GiacoBot/ESP32MP3/Software/src/AppState.h

#ifndef APP_STATE_H
#define APP_STATE_H

// Defines the current active screen or view of the application.
enum class AppScreen {
    SCREEN_BLUETOOTH_SELECTION,
    SCREEN_TRACK_SELECTION,
    SCREEN_NOW_PLAYING,
    SCREEN_VOLUME_CONTROL
};

#endif // APP_STATE_H
