GiacoBot/ESP32MP3/Software/src/DisplayManager.h

#ifndef DISPLAY_MANAGER_H
#define DISPLAY_MANAGER_H

#include <U8g2lib.h>
#include "settings.h"
#include "AppState.h"
#include "MusicPlayer.h"
#include "BluetoothManager.h"
#include "PlaylistManager.h"

class DisplayManager {
public:
    DisplayManager();
    bool initialize();

    // --- Core Update Method ---
    // This is now the main entry point for drawing, dispatched by the main loop.
    void update(AppScreen current_screen);

    // --- Setters for Managers ---
    void setMusicPlayer(MusicPlayer* player);
    void setBluetoothManager(BluetoothManager* btManager);
    void setPlaylistManager(PlaylistManager* playlistManager);

    // --- Setters for UI State ---
    // These will be called from the main loop to update the UI state
    void setBluetoothMenuState(int selected_index, int scroll_offset);
    void setPlaylistMenuState(int selected_index, int scroll_offset);

private:
    // --- Managers ---
    MusicPlayer* music_player;
    BluetoothManager* bluetooth_manager;
    PlaylistManager* playlist_manager;

    // --- Display & State ---
    U8G2_DISPLAY_TYPE u8g2;
    bool is_initialized;

    // --- UI State Variables ---
    int bt_menu_selected_index;
    int bt_menu_scroll_offset;
    int playlist_menu_selected_index;
    int playlist_menu_scroll_offset;

    // Internal state for tracking scroll direction
    int prev_bt_menu_selected_index;
    int prev_playlist_menu_selected_index;

    // Internal state for horizontal text scrolling
    unsigned long bt_last_selection_time;
    unsigned long bt_last_scroll_time;
    int bt_text_scroll_offset_pixels;
    unsigned long playlist_last_selection_time;
    unsigned long playlist_last_scroll_time;
    int playlist_text_scroll_offset_pixels;

    // Track name cache for playlist menu
    static const int PLAYLIST_VISIBLE_ITEMS = 4;
    String playlist_cached_names[PLAYLIST_VISIBLE_ITEMS];
    int playlist_cache_start_index;  // -1 = cache invalid

    // --- Drawing Methods ---
    void drawBluetoothMenu();
    void drawPlaylistMenu();
    void drawNowPlayingScreen();
    void drawVolumeScreen();

    // --- Cache Methods ---
    void updatePlaylistCache(int start_index);

    // --- "Now Playing" screen state tracking ---
    String last_displayed_track;
    bool last_bt_status;
    PlayerState last_player_state;
};

#endif // DISPLAY_MANAGER_H
